FugLong/OpenChord/m1/docs/README.md

# OpenChord M1 docs

- **[goals.md](goals.md)** — why M1 exists, and the hardware lock. Behavior is interaction.md. Status is build.md.
- **[interaction.md](interaction.md)** — behavior. Modes **Keys**, **Scale**, **Drums**. Keyswitches, not pads.
- **[build.md](build.md)** — order of work, and the **Where we are** status. Behavior stays in interaction.md.
- **[plugin.md](plugin.md)** — plugin v0 brief (lab harness: Pro / Smart). Superseded as a product spec by interaction.md.
- **[testbed.md](testbed.md)** — RP2040-Zero harness (and parked Seed notes).
- **[chord-engine.md](chord-engine.md)** — prototype music spec (Pro / Smart, stick never changes quality). Interaction plan replaces the stick rule in Play.
