FugLong/OpenChord/src/core/io/io_manager.cpp

#include "io_manager.h"
#include "pin_config.h"
#include "digital_manager.h"
#include "analog_manager.h"
#include "serial_manager.h"
#include "display_manager.h"
#include "storage_manager.h"
#include "power_manager.h"
#include <cstring>

IOManager::IOManager() 
    : hw_(nullptr), update_count_(0), last_update_time_(0), 
      power_mgr_(nullptr), last_analog_update_(0) {
    
    // Initialize system status
    memset(&status_, 0, sizeof(status_));
    status_.digital_healthy = true;
    status_.analog_healthy = true;
    status_.serial_healthy = true;
    status_.display_healthy = true;
    status_.storage_healthy = true;
}

IOManager::~IOManager() {
    Shutdown();
}

void IOManager::Init(daisy::DaisySeed* hw) {
    hw_ = hw;
    
    // Initialize all sub-managers (static allocation)
    digital_.Init(hw);
    analog_.Init(hw);
    serial_.Init(hw);
    display_.Init(hw);
    storage_.Init(hw);
    
    // Reset update counters
    update_count_ = 0;
    last_update_time_ = 0;
    
    // Clear any previous errors
    ClearErrors();
}

void IOManager::Update() {
    if (!hw_) return;
    
    uint32_t now = hw_->system.GetNow();
    
    // Always update digital manager - it needs high frequency for proper debouncing
    // Power savings come from other subsystems, not input responsiveness
    digital_.Update();
    
    // Update analog manager conditionally (power-aware)
    if (!power_mgr_ || power_mgr_->ShouldUpdateADC(last_analog_update_)) {
    analog_.Update();
        last_analog_update_ = now;
    }
    
    // Serial, display, and storage are updated less frequently or on-demand
    serial_.Update();
    display_.Update();
    storage_.Update();
    
    // Update system status
    UpdateSystemStatus();
    
    // Handle any errors that occurred
    HandleErrors();
    
    // Update counters
    update_count_++;
    last_update_time_ = now;
}

void IOManager::Shutdown() {
    if (!hw_) return;
    
    // Shutdown all sub-managers
    digital_.Shutdown();
    analog_.Shutdown();
    serial_.Shutdown();
    display_.Shutdown();
    storage_.Shutdown();
    
    hw_ = nullptr;
}

bool IOManager::IsHealthy() const {
    return status_.digital_healthy && 
           status_.analog_healthy && 
           status_.serial_healthy && 
           status_.display_healthy && 
           status_.storage_healthy &&
           status_.error_count == 0;
}

const SystemStatus& IOManager::GetStatus() const {
    return status_;
}

void IOManager::ReportError(IOComponent component, const char* error) {
    status_.error_count++;
    status_.last_error_time = hw_ ? hw_->system.GetNow() : 0;
    
    // Mark the appropriate component as unhealthy
    switch (component) {
        case IOComponent::DIGITAL:
            status_.digital_healthy = false;
            break;
        case IOComponent::ANALOG:
            status_.analog_healthy = false;
            break;
        case IOComponent::SERIAL:
            status_.serial_healthy = false;
            break;
        case IOComponent::DISPLAY:
            status_.display_healthy = false;
            break;
        case IOComponent::STORAGE:
            status_.storage_healthy = false;
            break;
    }
    
    // TODO: Add proper error logging when we implement it
    // For now, we could use the Daisy Seed's serial output for debugging
}

void IOManager::ClearErrors() {
    status_.error_count = 0;
    status_.last_error_time = 0;
    status_.digital_healthy = true;
    status_.analog_healthy = true;
    status_.serial_healthy = true;
    status_.display_healthy = true;
    status_.storage_healthy = true;
}

void IOManager::UpdateSystemStatus() {
    // Check health of each sub-manager
    status_.digital_healthy = digital_.IsHealthy();
    status_.analog_healthy = analog_.IsHealthy();
    status_.serial_healthy = serial_.IsHealthy();
    status_.display_healthy = display_.IsHealthy();
    status_.storage_healthy = storage_.IsHealthy();
}

void IOManager::HandleErrors() {
    // TODO: Implement error recovery strategies
    // For now, just track errors in the status
    // Later we can add:
    // - Automatic retry mechanisms
    // - Fallback modes
    // - User notifications
    // - Error logging
} 
