FugLong/OpenChord/src/core/ui/debug_screen.cpp

#include "debug_screen.h"
#include "../io/button_input_handler.h"
#include <algorithm>

namespace OpenChord {

DebugScreen::DebugScreen()
    : display_(nullptr)
    , input_manager_(nullptr)
    , current_view_index_(-1)
    , enabled_(true)
    , render_interval_ms_(100)  // 10 FPS default
    , last_render_time_(0)
    , prev_input_pressed_(false)
    , prev_record_pressed_(false)
    , combo_hold_time_(0)
    , already_toggled_this_cycle_(false)
{
}

DebugScreen::~DebugScreen() {
    views_.clear();
}

void DebugScreen::Init(DisplayManager* display, InputManager* input_manager) {
    display_ = display;
    input_manager_ = input_manager;
    
    if (views_.empty()) {
        current_view_index_ = -1;
    } else {
        current_view_index_ = 0;
    }
    
    last_render_time_ = 0;
    prev_input_pressed_ = false;
    prev_record_pressed_ = false;
    combo_hold_time_ = 0;
    already_toggled_this_cycle_ = false;
}

void DebugScreen::AddView(const char* name, DebugRenderFunc render_func) {
    if (name && render_func) {
        views_.push_back(DebugView(name, render_func));
        
        // If this is the first view, set it as current
        if (current_view_index_ == -1 && views_.size() == 1) {
            current_view_index_ = 0;
        }
    }
}

void DebugScreen::Update() {
    // Always handle toggle combo, even when disabled (allows toggling on)
    HandleToggleCombo();
    
    // Only process navigation and rendering if enabled
    if (!enabled_ || !display_ || !display_->IsHealthy()) {
        return;
    }
    
    if (views_.empty() || current_view_index_ < 0 || 
        current_view_index_ >= static_cast<int>(views_.size())) {
        return;
    }
    
    // Handle navigation
    HandleNavigation();
    
    // Render at configured interval
    if (last_render_time_ >= render_interval_ms_) {
        RenderCurrentView();
        last_render_time_ = 0;
    } else {
        last_render_time_++;
    }
}

void DebugScreen::NextView() {
    if (views_.empty()) return;
    current_view_index_ = (current_view_index_ + 1) % static_cast<int>(views_.size());
}

void DebugScreen::PreviousView() {
    if (views_.empty()) return;
    current_view_index_--;
    if (current_view_index_ < 0) {
        current_view_index_ = static_cast<int>(views_.size()) - 1;
    }
}

void DebugScreen::SetView(int index) {
    if (views_.empty() || index < 0 || index >= static_cast<int>(views_.size())) {
        return;
    }
    current_view_index_ = index;
}

const char* DebugScreen::GetCurrentViewName() const {
    if (current_view_index_ >= 0 && current_view_index_ < static_cast<int>(views_.size())) {
        return views_[current_view_index_].name;
    }
    return nullptr;
}

void DebugScreen::Render(DisplayManager* display) {
    if (!display || !display->IsHealthy()) {
        RenderCurrentView();  // Fallback to internal render if display not provided
        return;
    }
    
    // Use provided display instead of stored one
    RenderCurrentViewInternal(display);
}

void DebugScreen::RenderCurrentView() {
    if (!display_ || !display_->IsHealthy() || views_.empty()) {
        return;
    }
    
    RenderCurrentViewInternal(display_);
}

void DebugScreen::RenderCurrentViewInternal(DisplayManager* display) {
    if (!display || !display->IsHealthy() || views_.empty()) {
        return;
    }
    
    if (current_view_index_ < 0 || current_view_index_ >= static_cast<int>(views_.size())) {
        return;
    }
    
    const DebugView& view = views_[current_view_index_];
    if (view.render) {
        // Note: Display clearing and Update() are now handled by UIManager
        // Just call the render function - it should render to content area (offset by 10 pixels)
        view.render(display);
    }
}
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
